terrafirma2021/Yamaha-DataLogger/Newpids_n.jpg

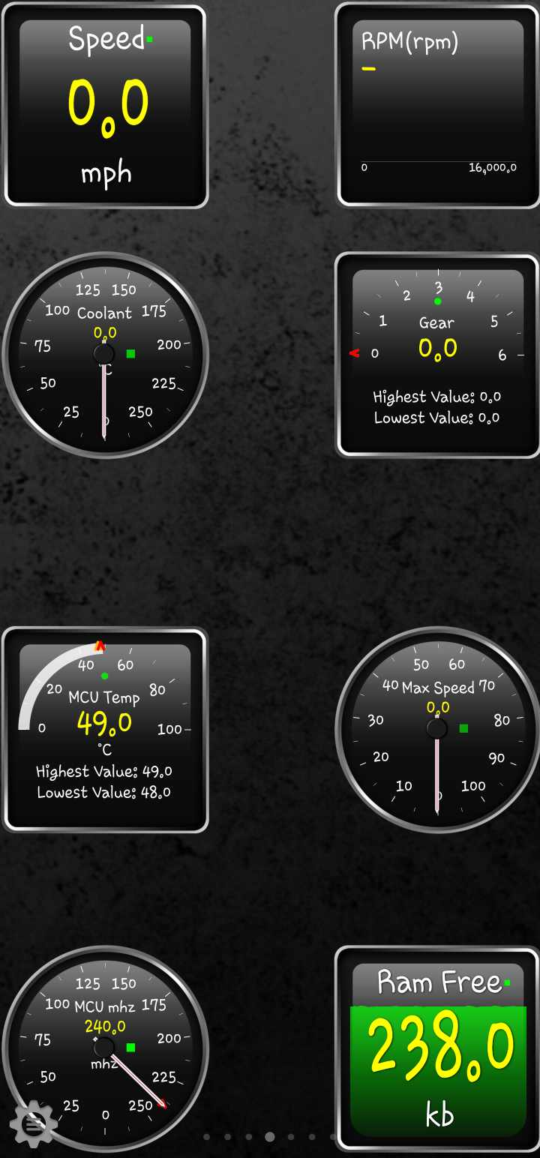
Newpids_n.jpg
