terrafirma2021/Yamaha-DataLogger/realdash/Screenshot_RD.jpg

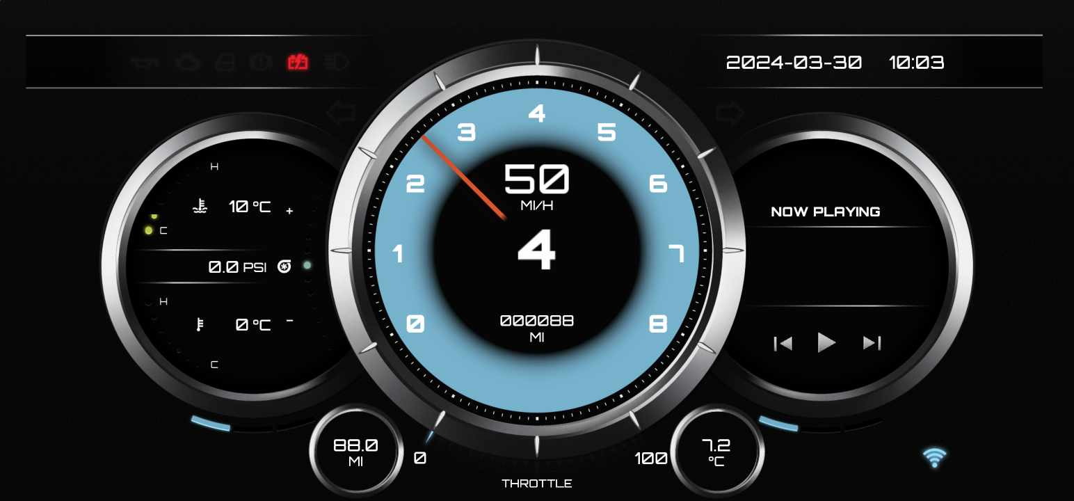
realdash/Screenshot_RD.jpg
