terrafirma2021/Yamaha-DataLogger/3d printed case/20240402_010137.jpg

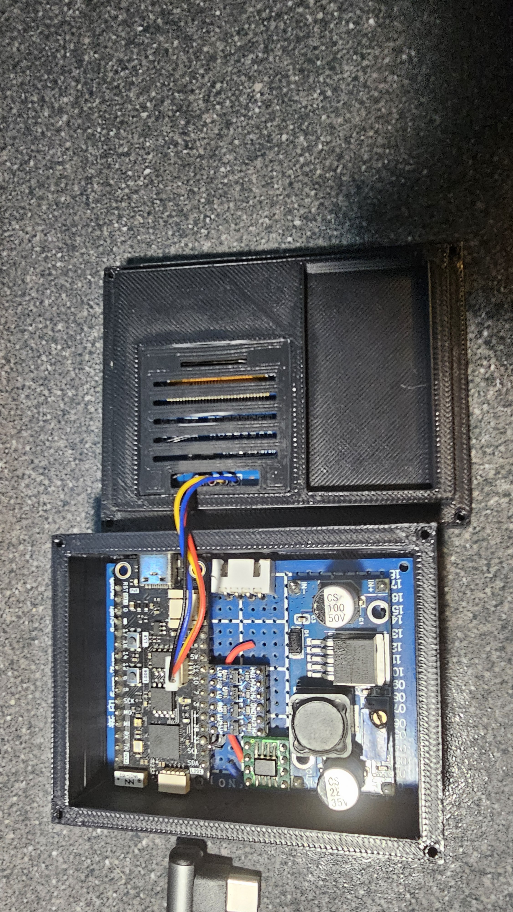
3d printed case/20240402_010137.jpg
